K4zuki/usb4x3hub/doc/images/USB4x3HUB_r04-a30fd1f_meas_r+090.png

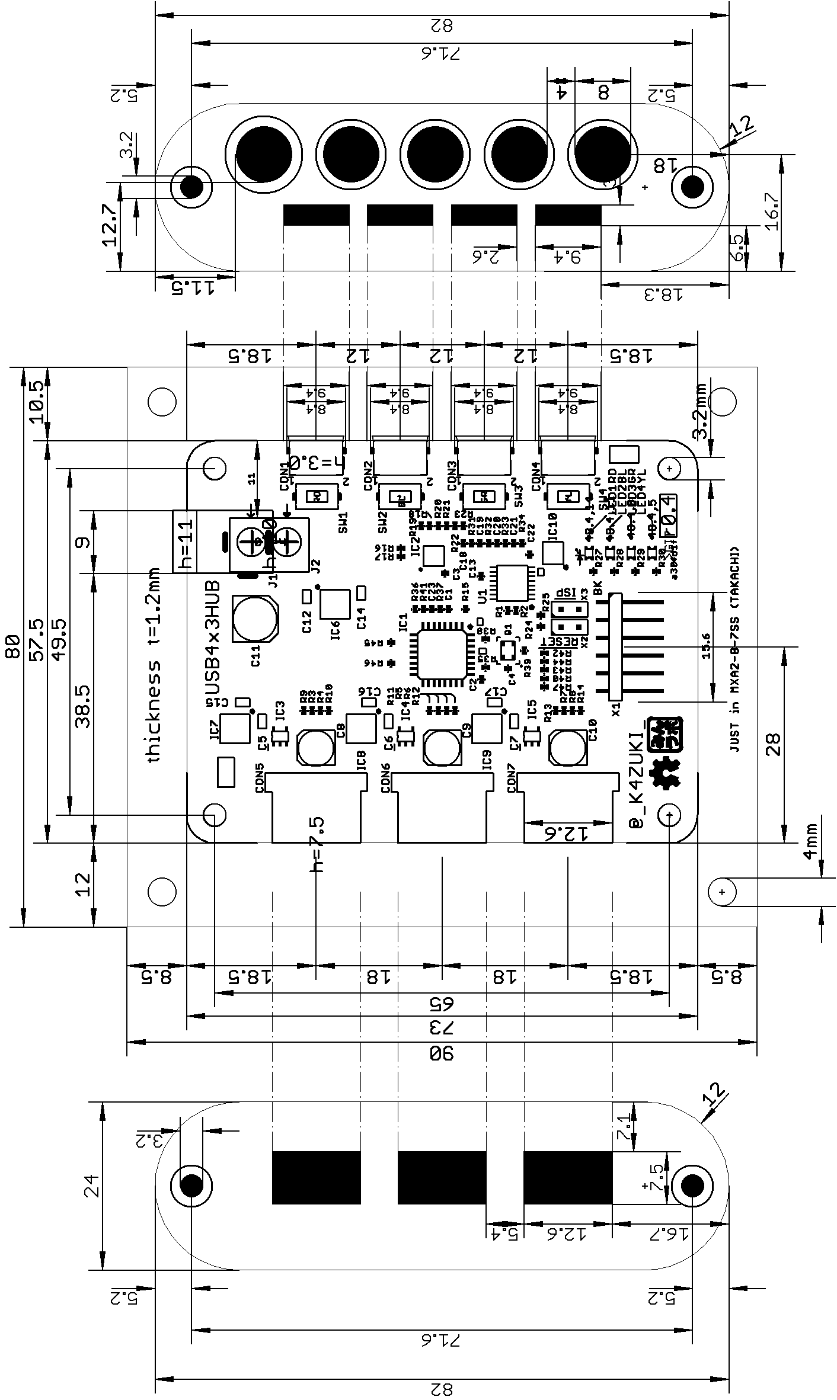
doc/images/USB4x3HUB_r04-a30fd1f_meas_r+090.png
