K4zuki/usb4x3hub/doc/images/USB4x3HUB_r04_LPC812.png

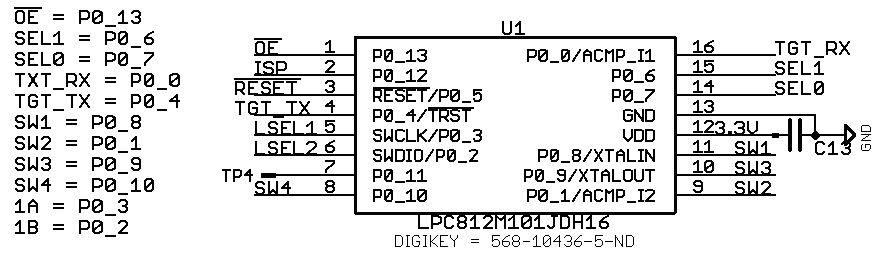
doc/images/USB4x3HUB_r04_LPC812.png
