K4zuki/usb4x3hub/doc/images/USB4x3HUB_r04_sch.png

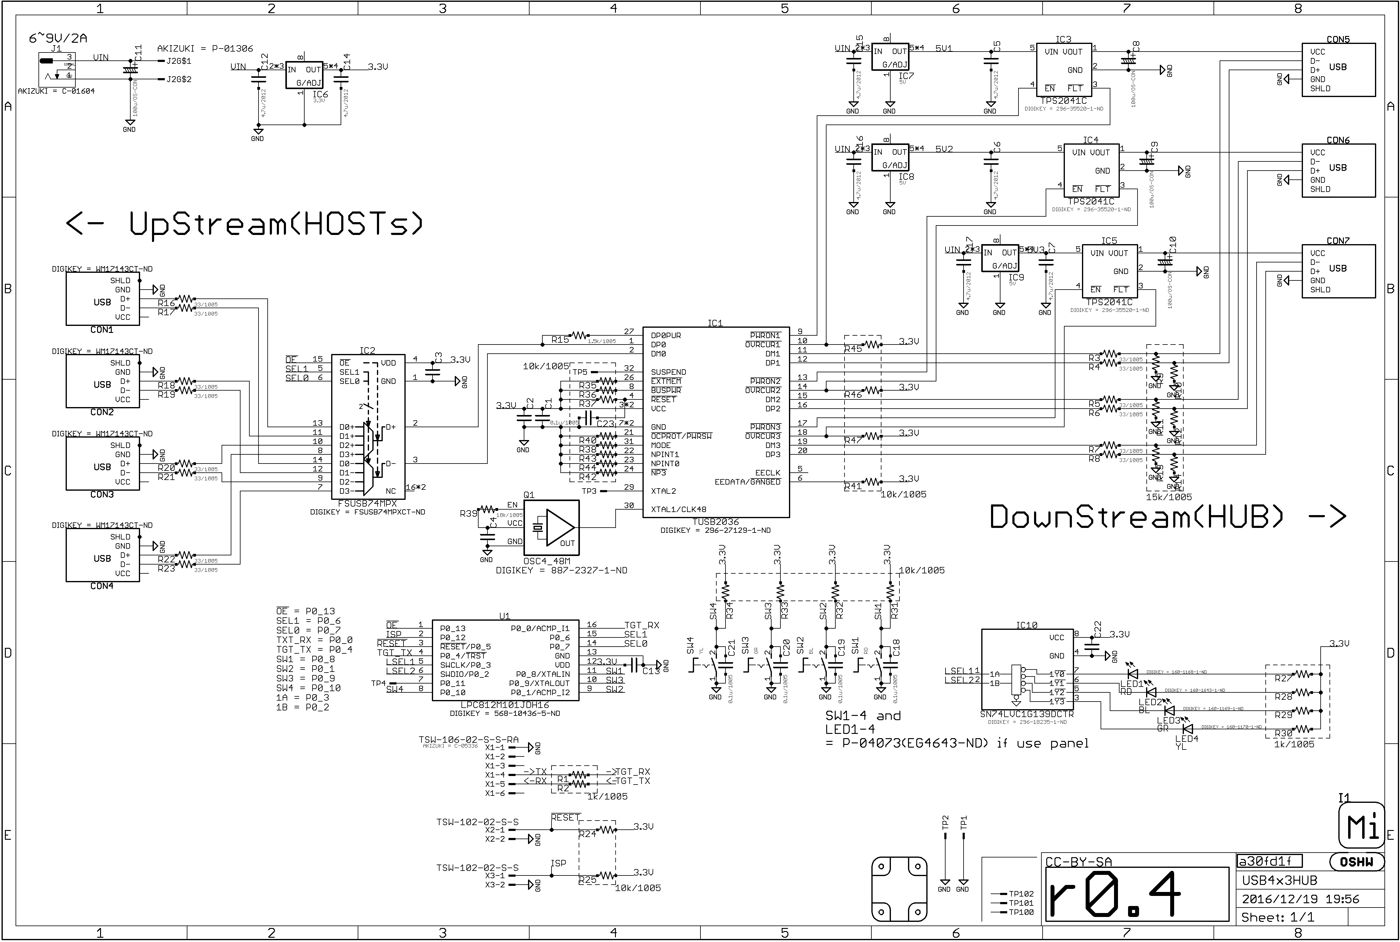
doc/images/USB4x3HUB_r04_sch.png
