K4zuki/usb4x3hub/doc/images/USB4x3HUB_r04_sch_r+090.png

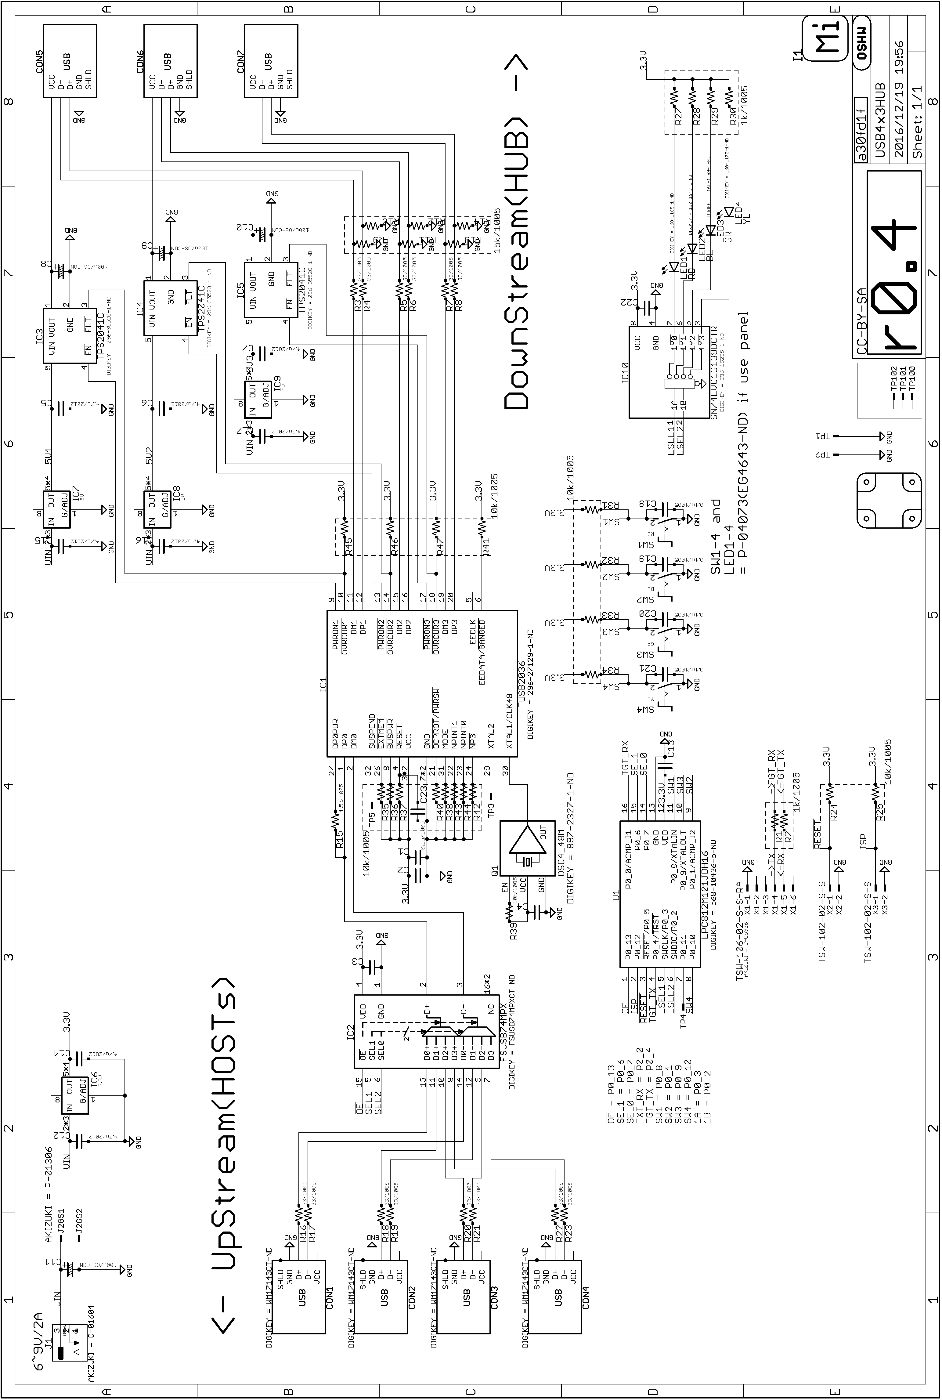
doc/images/USB4x3HUB_r04_sch_r+090.png
