K4zuki/usb4x3hub/doc/images/USB4x3HUBr1.png

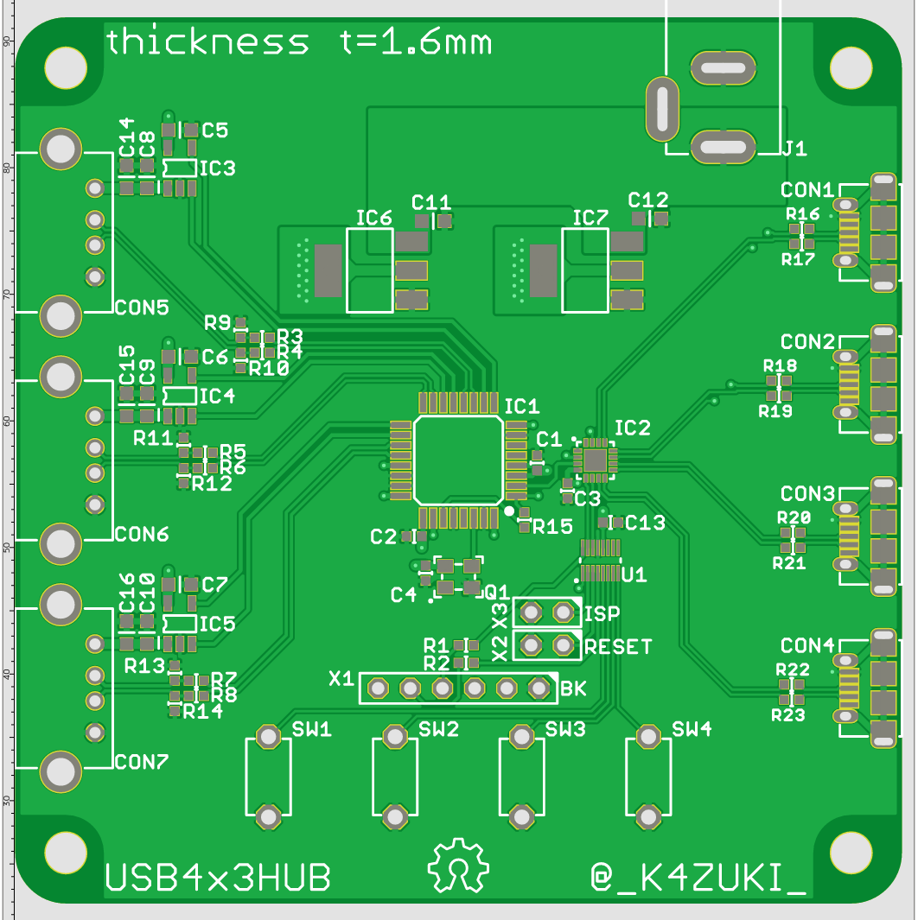
doc/images/USB4x3HUBr1.png
