K4zuki/usb4x3hub/doc/images/USB4x3HUBr03_placement.png

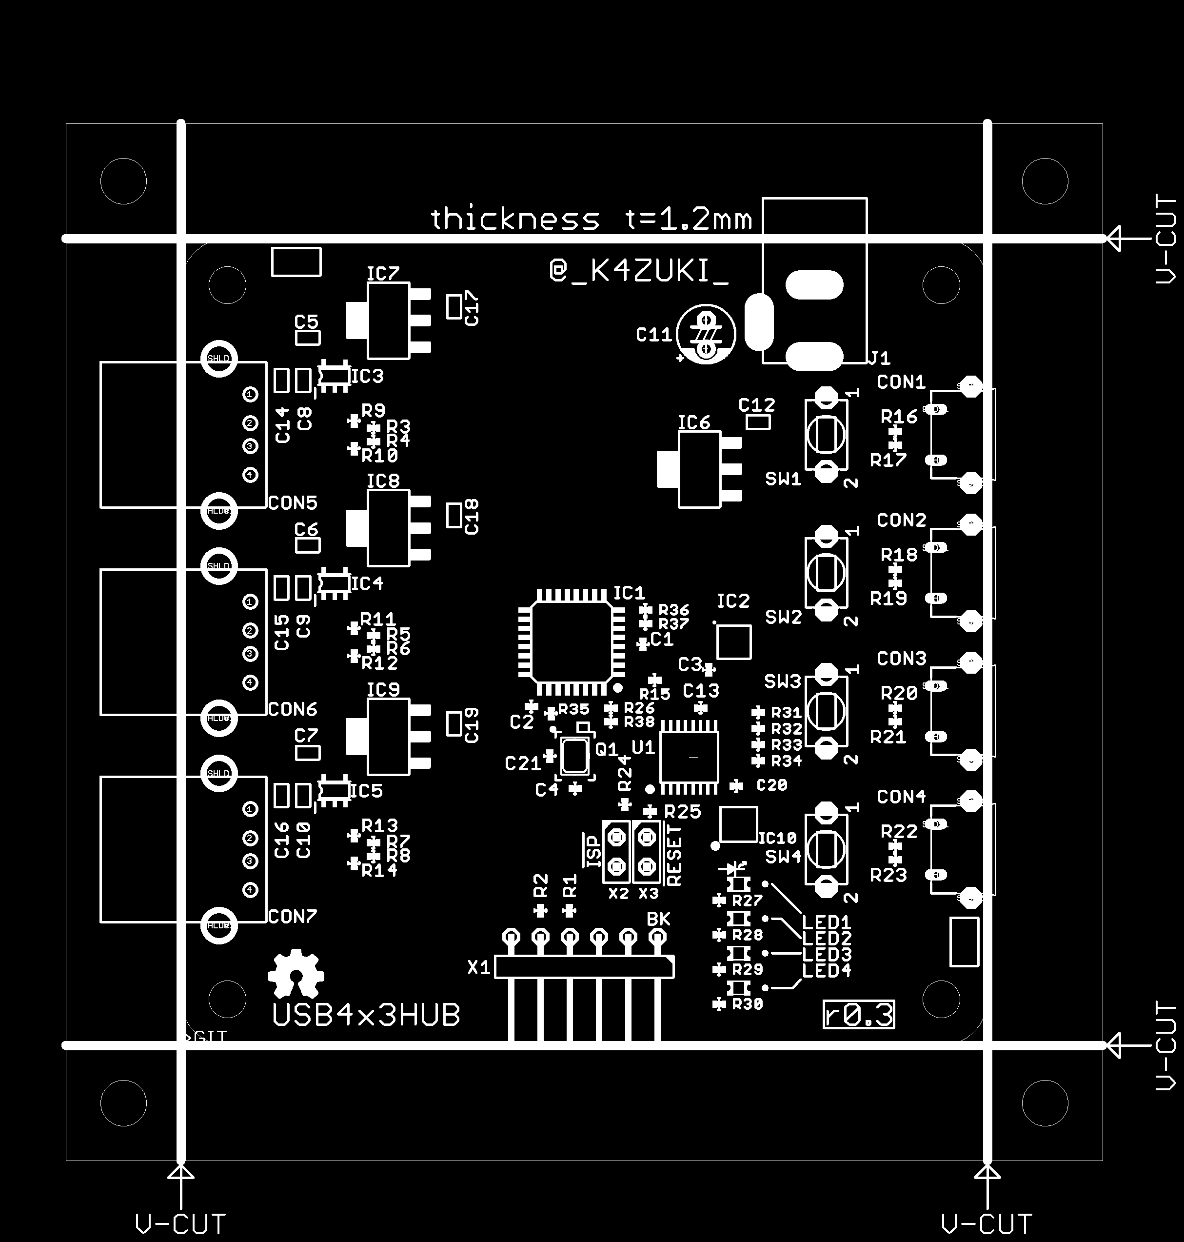
doc/images/USB4x3HUBr03_placement.png
